jonathansbidesign/bamms/STL_FIles/material_shaper_V1.stl

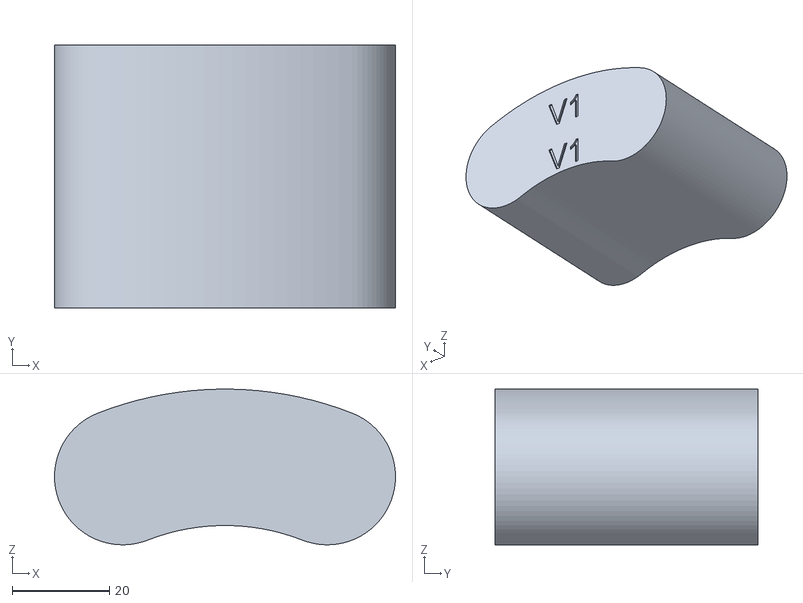
[picture p15: CAD file, 2026-07-05]
STL_FIles/material_shaper_V1.stl
70.0 x 54.0 x 32.0
